wuelaineyuan-bit/MUSICGAME/Schematic/LED Matrix.kicad_sch

## KiCad design Schematic/LED Matrix.kicad_sch (2026-06-20)

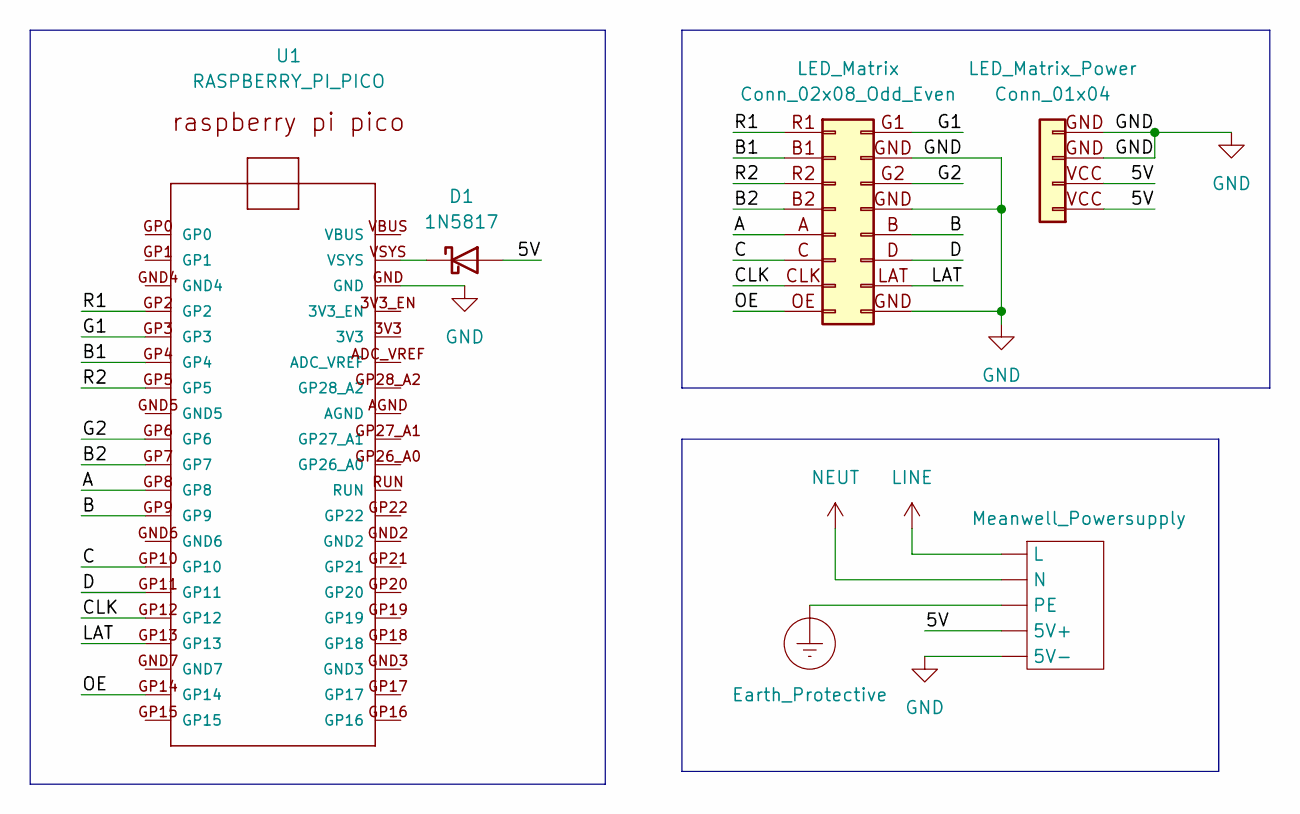
[picture p15: schematic LED Matrix.kicad_sch]

Parts:
D1: 1N5817; D_DO-41_SOD81_P10.16mm_Horizontal
LED_Matrix: Conn_02x08_Odd_Even
LED_Matrix_Power: Conn_01x04
Meanwell_Powersupply: (no value)
U1: RASPBERRY_PI_PICO

Connections:
5V: D1.2 (A), LED_Matrix_Power.VCC (Pin_1), Meanwell_Powersupply.
A: LED_Matrix.A (Pin_9), U1.GP8
B: LED_Matrix.B (Pin_10), U1.GP9
B1: LED_Matrix.B1 (Pin_3), U1.GP4
B2: LED_Matrix.B2 (Pin_7), U1.GP7
C: LED_Matrix.C (Pin_11), U1.GP10
CLK: LED_Matrix.CLK (Pin_13), U1.GP12
D: LED_Matrix.D (Pin_12), U1.GP11
Earth_Protective: Meanwell_Powersupply.
G1: LED_Matrix.G1 (Pin_2), U1.GP3
G2: LED_Matrix.G2 (Pin_6), U1.GP6
GND: LED_Matrix.GND (Pin_4), LED_Matrix_Power.GND (Pin_3), Meanwell_Powersupply., U1.GND
LAT: LED_Matrix.LAT (Pin_14), U1.GP13
LINE: Meanwell_Powersupply.
NEUT: Meanwell_Powersupply.
unnamed: D1.1 (K), U1.VSYS
OE: LED_Matrix.OE (Pin_15), U1.GP14
R1: LED_Matrix.R1 (Pin_1), U1.GP2
R2: LED_Matrix.R2 (Pin_5), U1.GP5
